dslik/powersim/1840A/1840-0101/latest/pcb_top.png

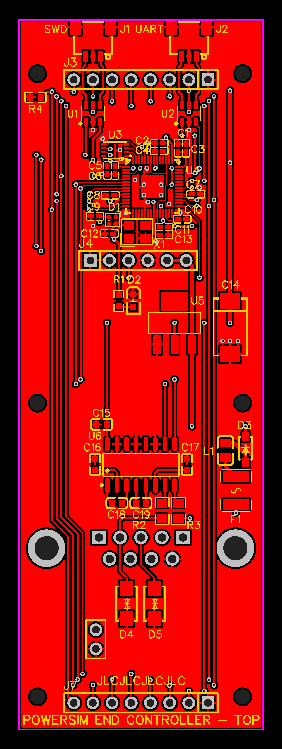
1840A/1840-0101/latest/pcb_top.png
