dslik/powersim/1841A/1841-0101/latest/pcb_top.png

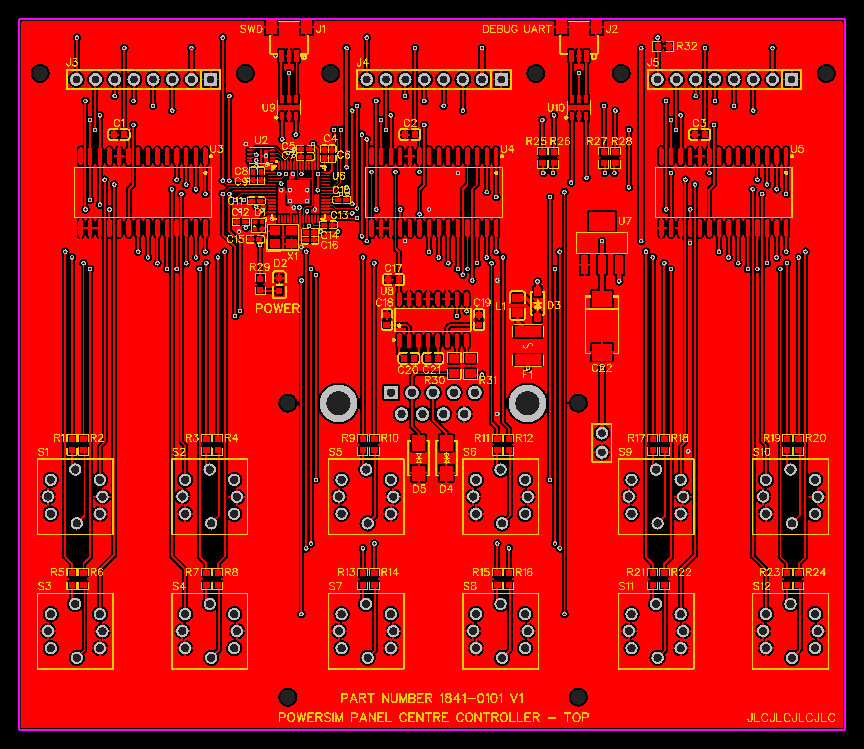
1841A/1841-0101/latest/pcb_top.png
