dslik/powersim/1850A/1850-0201/latest/pcb_top.png

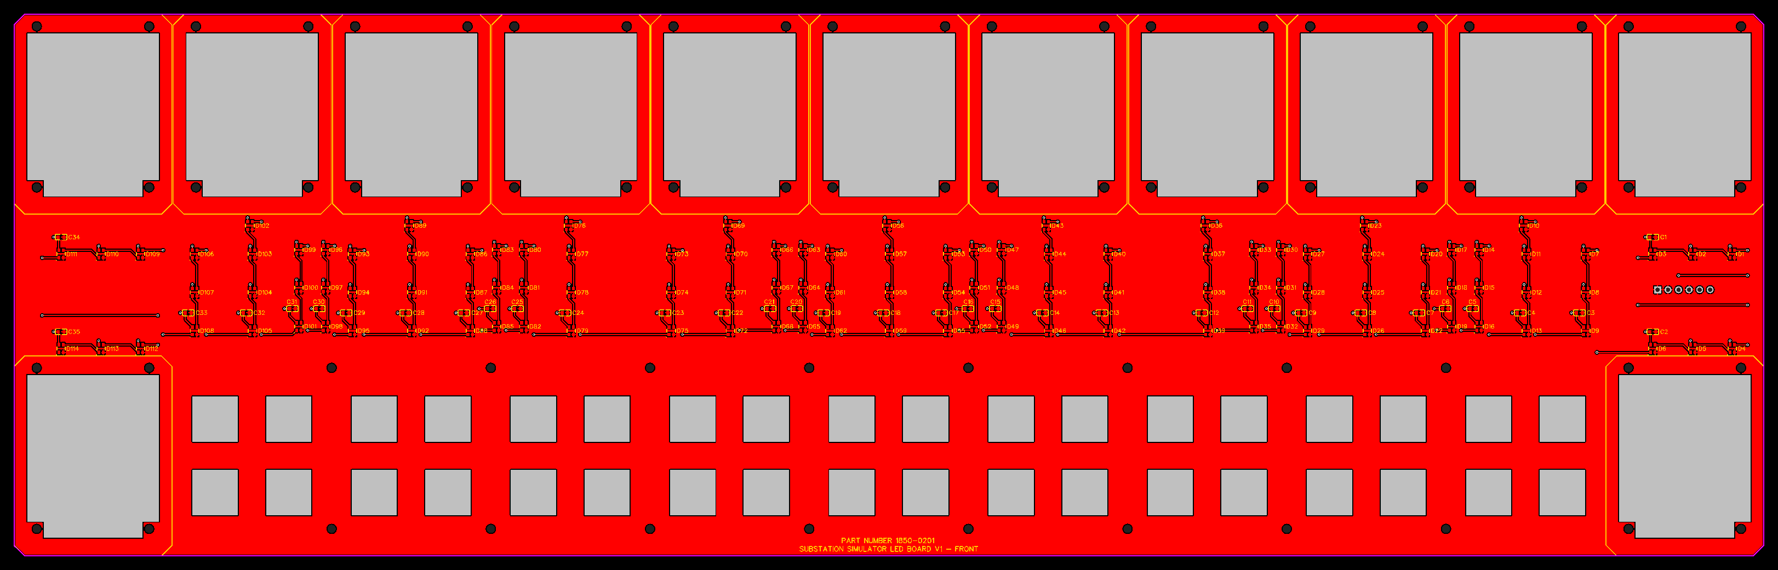
1850A/1850-0201/latest/pcb_top.png
