dslik/powersim/1850A/1850-0201/V1.2/pcb_bottom.png

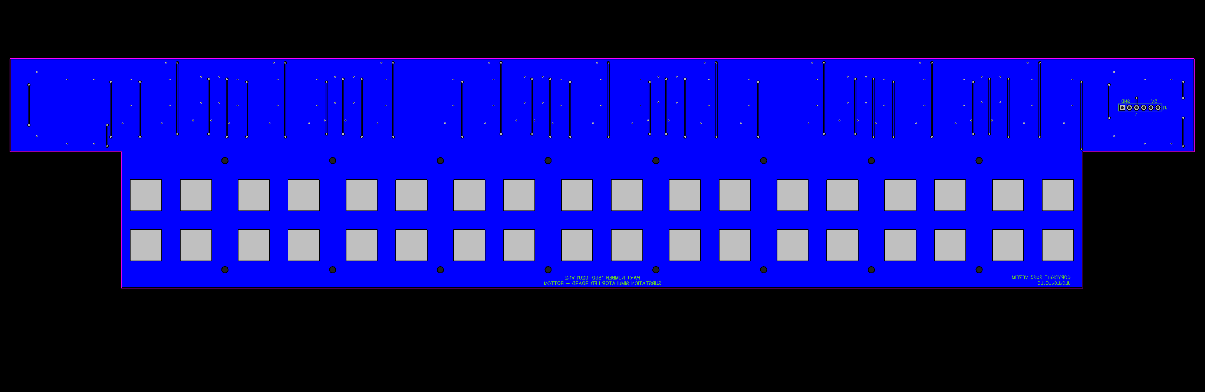
1850A/1850-0201/V1.2/pcb_bottom.png
