dslik/powersim/1850A/1850-0201/V1.2/Produce_DanZhi.SMT_Snapshot.Top.2154951A_Y738.SMT02308291374351.png

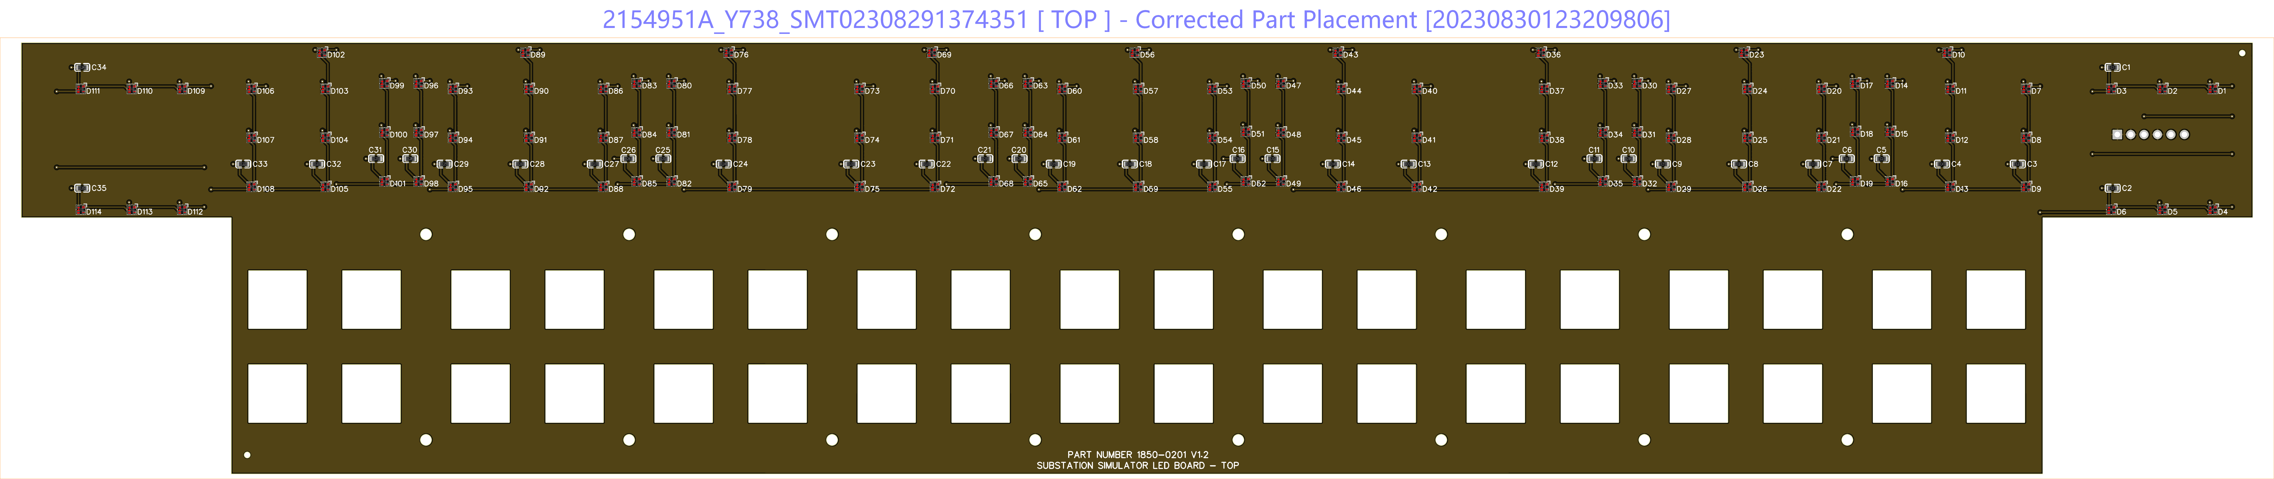
1850A/1850-0201/V1.2/Produce_DanZhi.SMT_Snapshot.Top.2154951A_Y738.SMT02308291374351.png
