dslik/powersim/1850A/1850-0202/latest/pcb_top.png

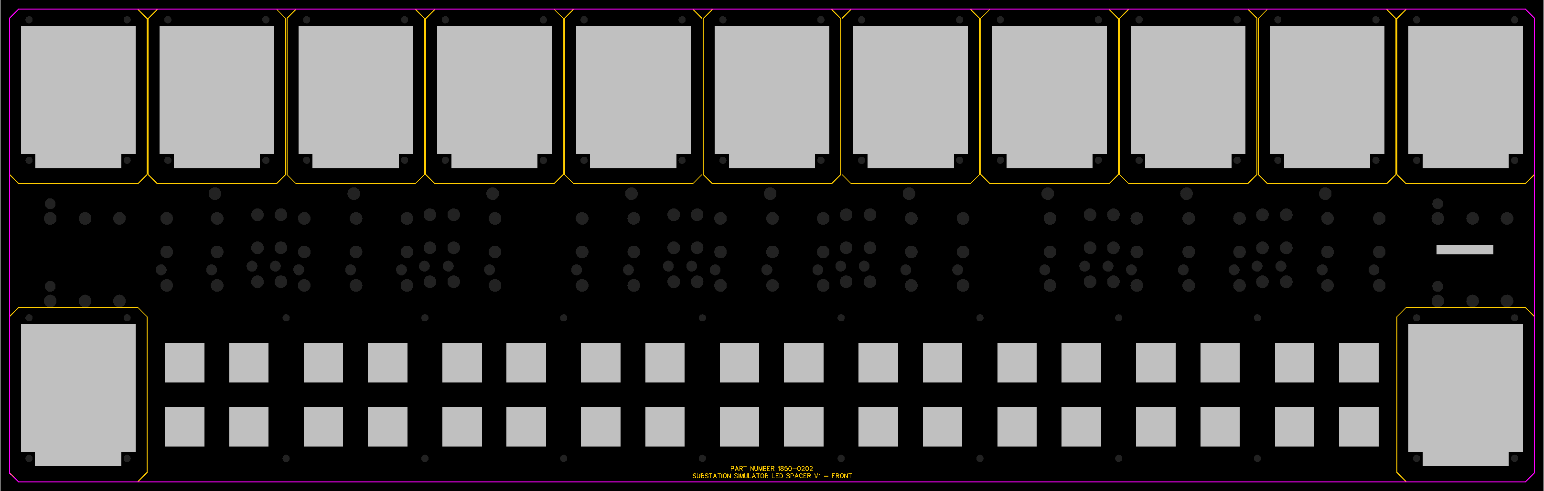
1850A/1850-0202/latest/pcb_top.png
