dslik/powersim/1850A/1850-0203/v0.2/pcb_top.png

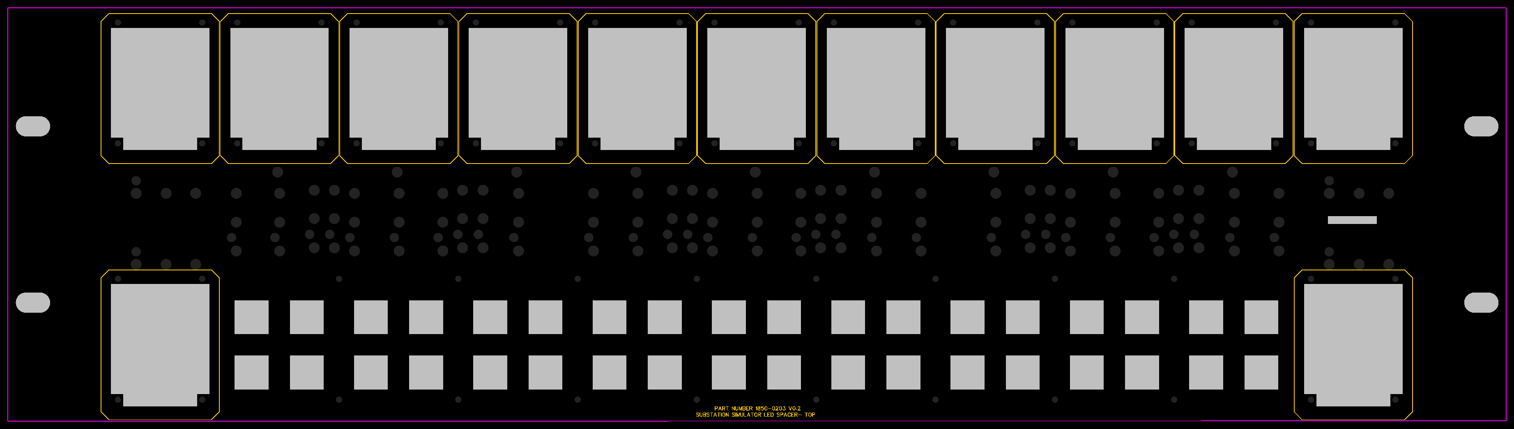
1850A/1850-0203/v0.2/pcb_top.png
