dslik/powersim/1851A/1851-0103/latest/pcb_top.png

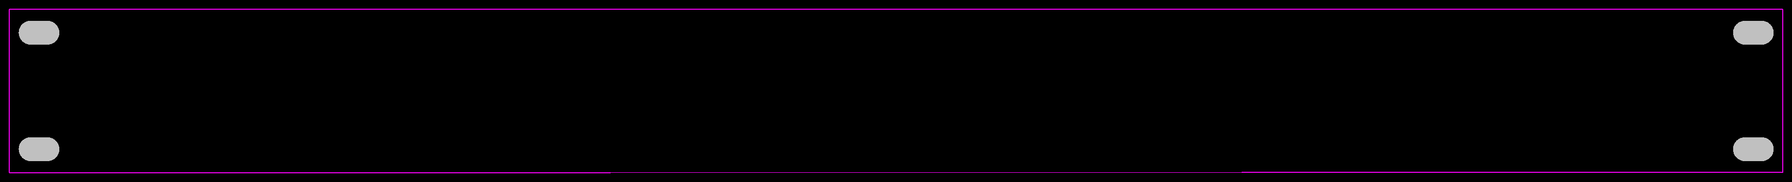
1851A/1851-0103/latest/pcb_top.png
