dslik/powersim/1852A/1852-0101/V0.2/pcb_bottom.png

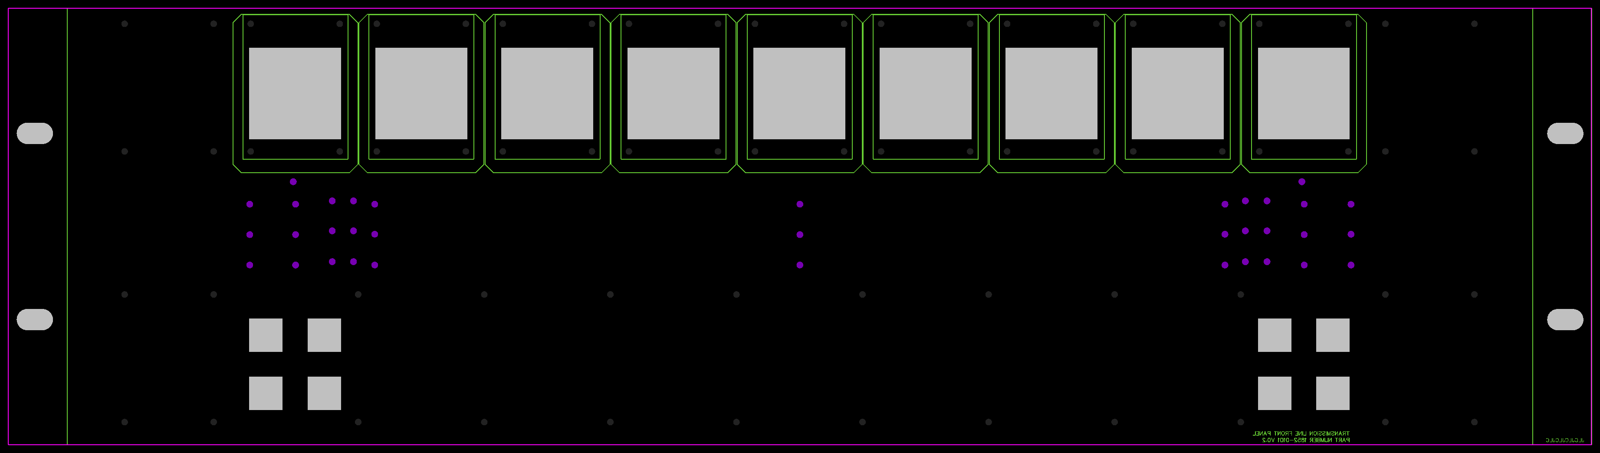
1852A/1852-0101/V0.2/pcb_bottom.png
