dslik/powersim/1853A/1853-0101/latest/pcb_top.png

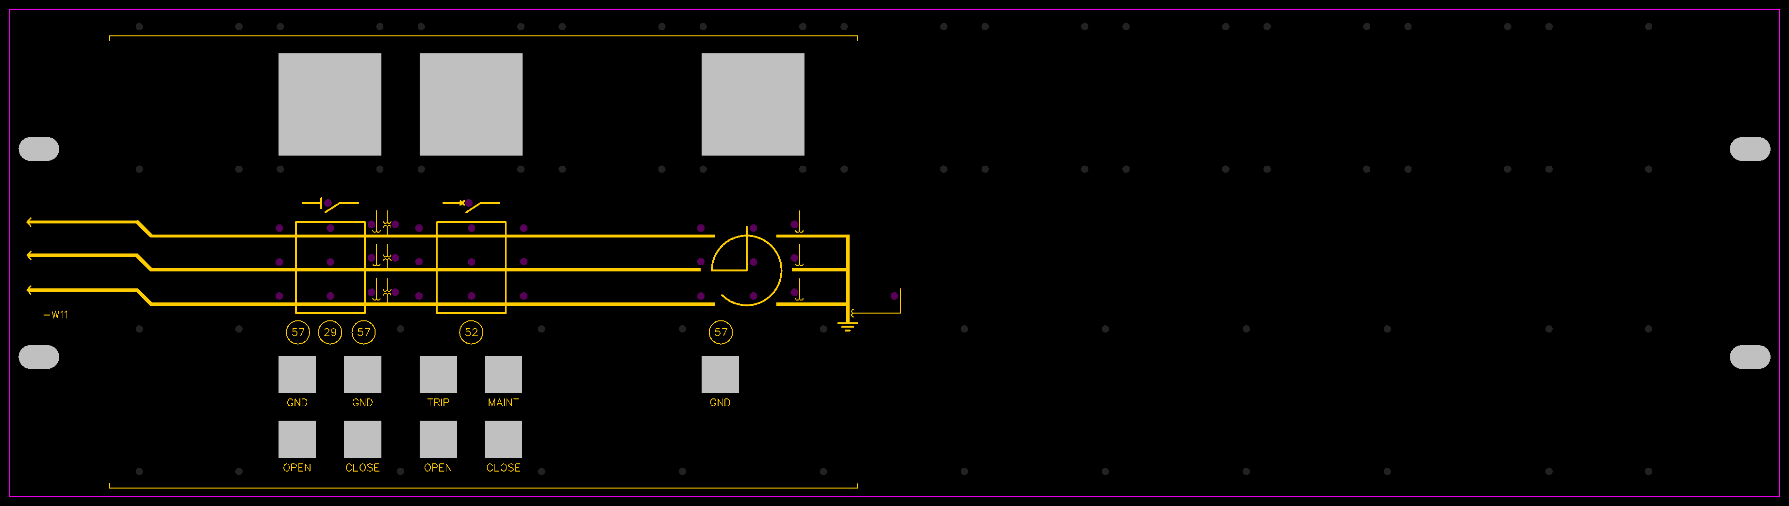
1853A/1853-0101/latest/pcb_top.png
