dslik/powersim/1854A/1854-0101/latest/pcb_top.png

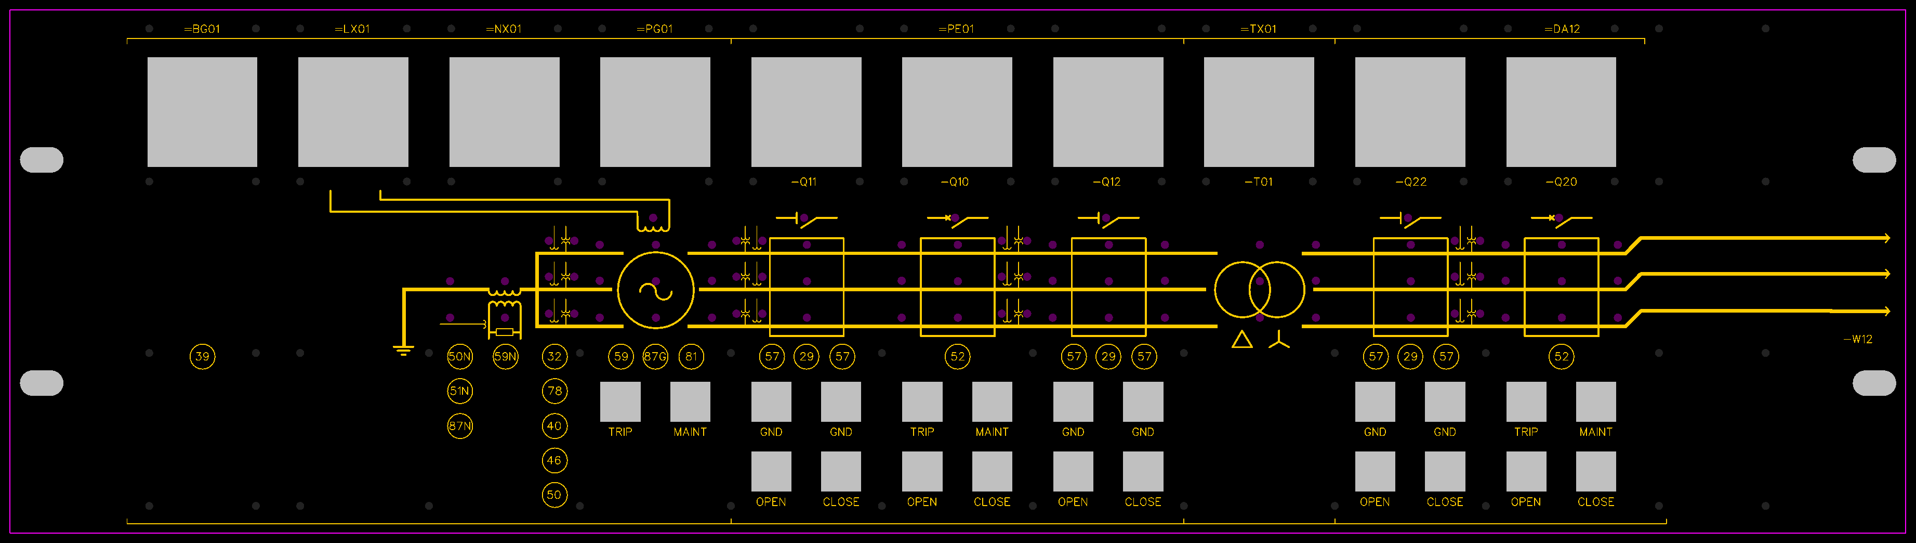
1854A/1854-0101/latest/pcb_top.png
