dslik/powersim/1859A/1859-0101/latest/pcb_top.png

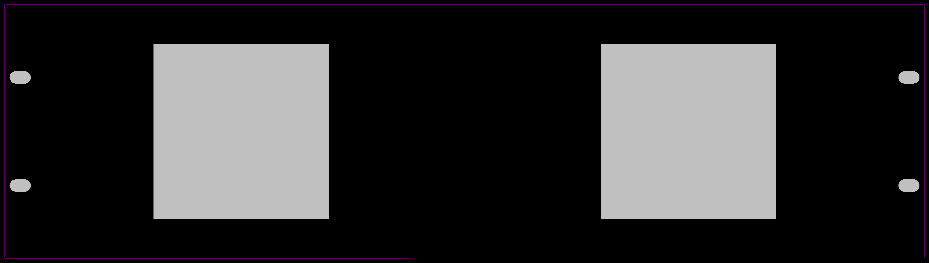
1859A/1859-0101/latest/pcb_top.png
