dslik/powersim/1859A/1859-0101/V0.2/pcb_top.png

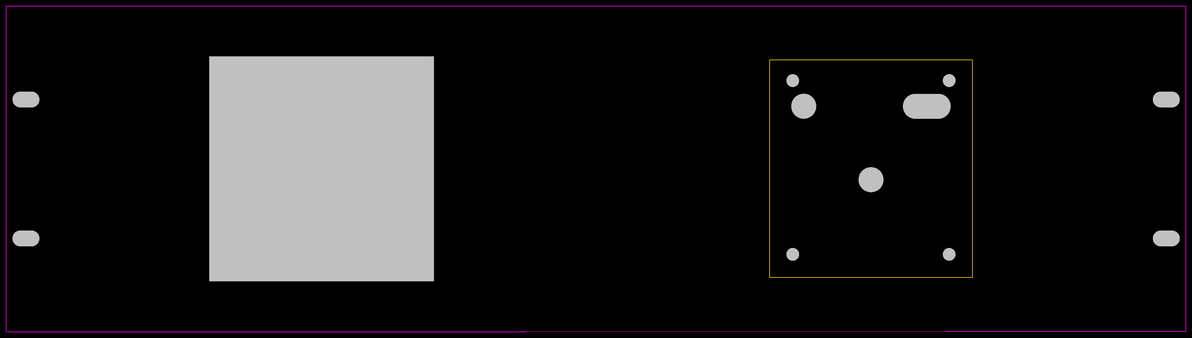
1859A/1859-0101/V0.2/pcb_top.png
