dslik/powersim/1870A/1870-0101/latest/pcb_top.png

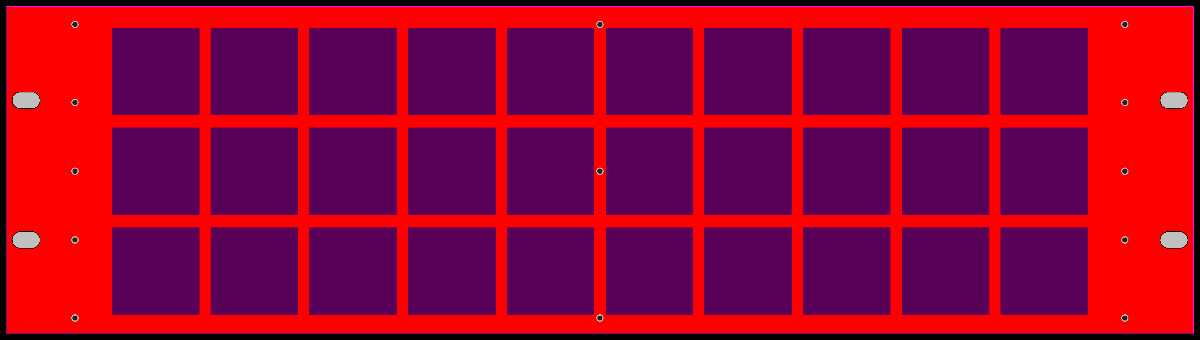
1870A/1870-0101/latest/pcb_top.png
