dslik/powersim/1870A/1870-0101/V0.2/pcb_top.png

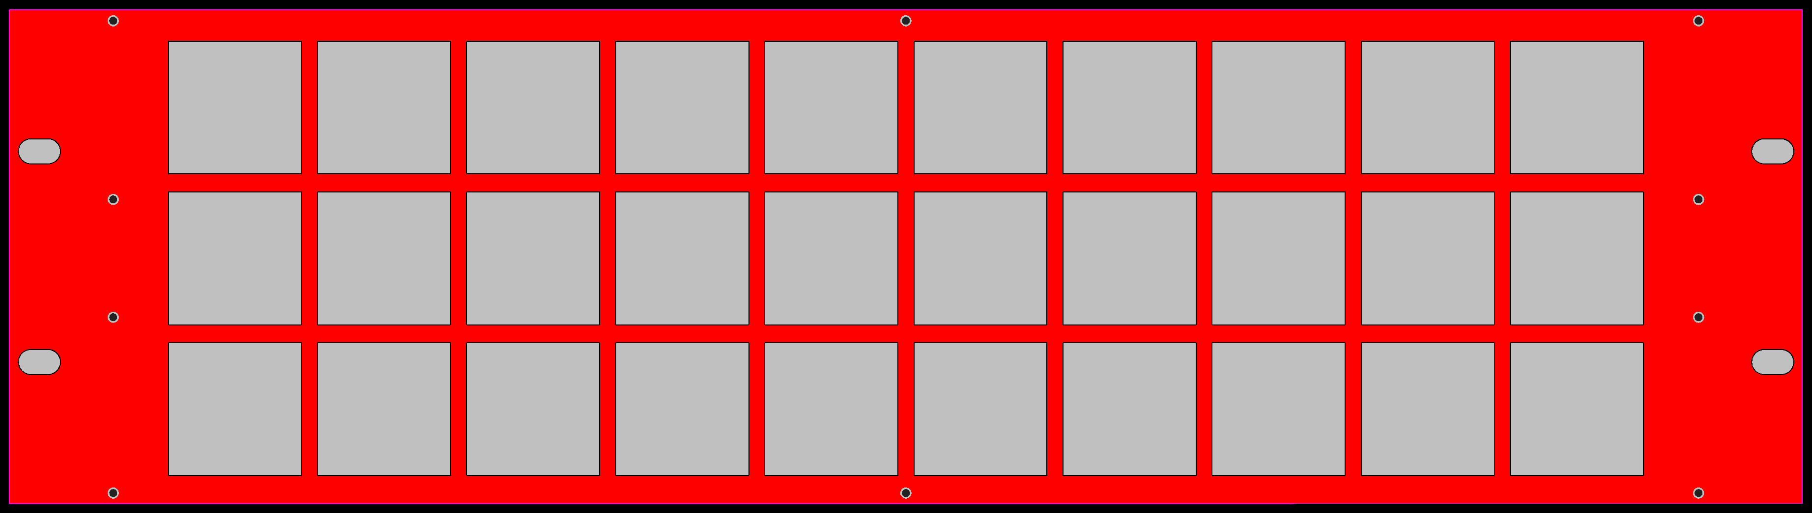
1870A/1870-0101/V0.2/pcb_top.png
