dslik/powersim/1870A/1870-0102/V0.3/pcb_bottom.png

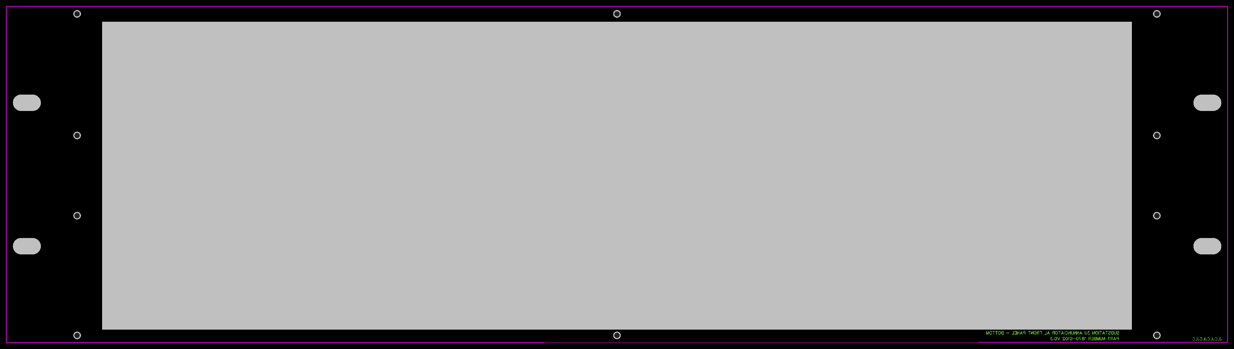
1870A/1870-0102/V0.3/pcb_bottom.png
