dslik/powersim/1870A/1870-0103/latest/pcb_top.png

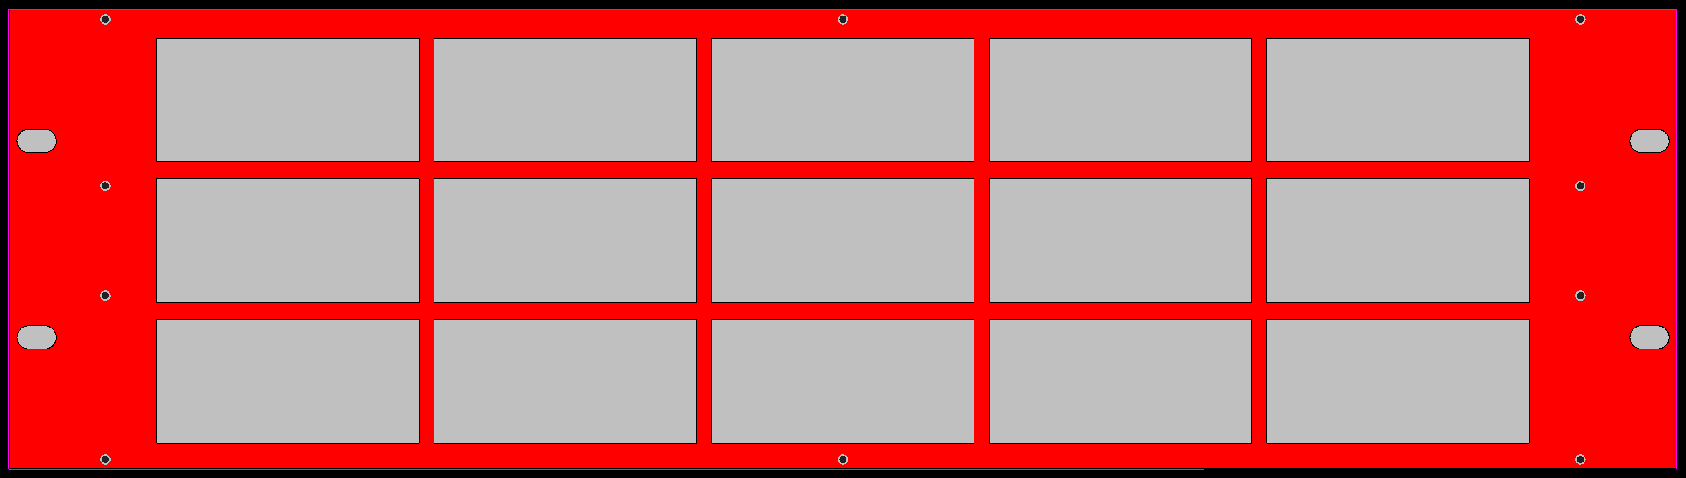
1870A/1870-0103/latest/pcb_top.png
