dslik/powersim/1870A/1870-0201/latest/pcb_top.png

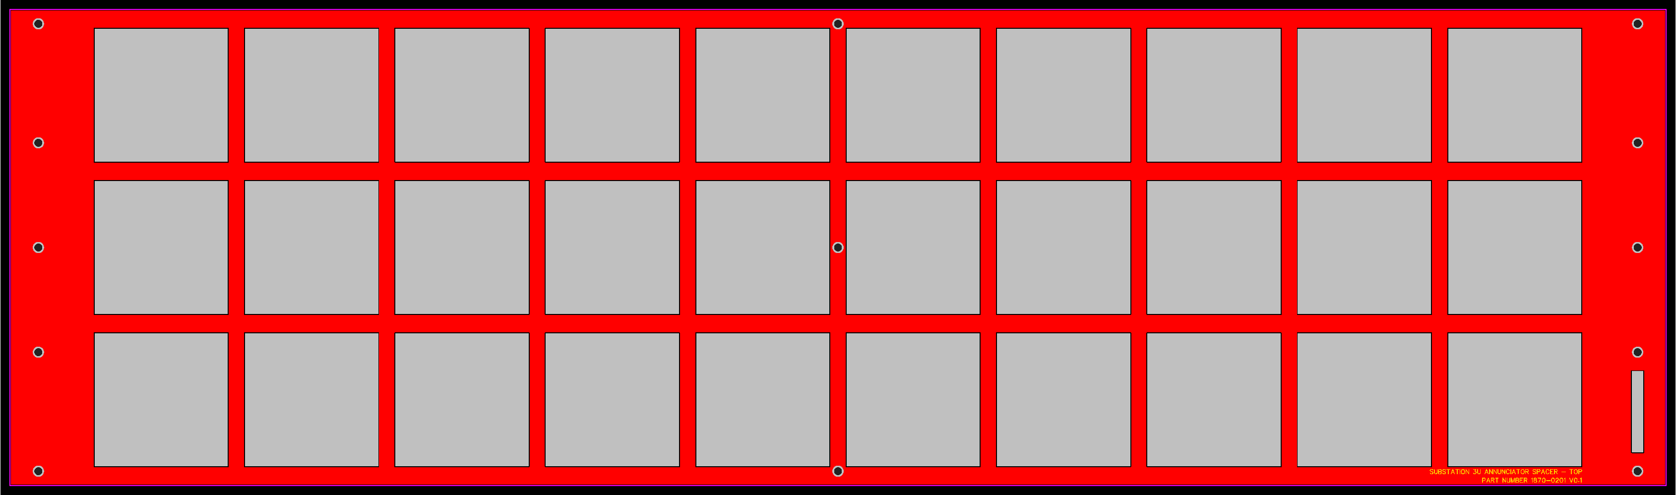
1870A/1870-0201/latest/pcb_top.png
