dslik/powersim/1870A/1870-0203/latest/pcb_bottom.png

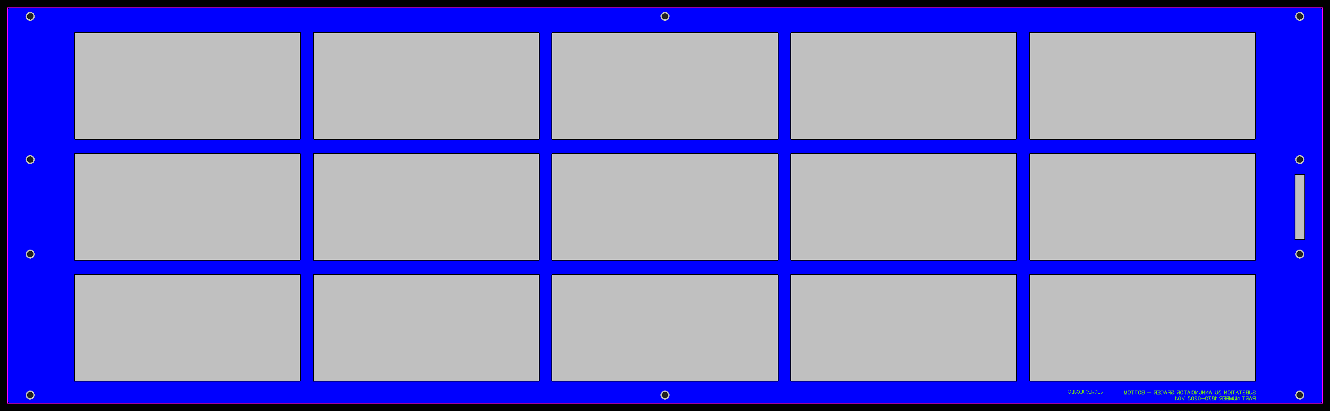
1870A/1870-0203/latest/pcb_bottom.png
