dslik/powersim/1841A/1841-9101/hmi.c

// ---------------------------------------------------------------------------------
// Front panel display routines
// ---------------------------------------------------------------------------------
// Routines for displaying user interfaces on various power simulator front panels
// ---------------------------------------------------------------------------------
// SPDX-FileCopyrightText: Copyright 2023 David Slik (VE7FIM)
// SPDX-FileAttributionText: https://github.com/dslik/powersim/
// SPDX-License-Identifier: CERN-OHL-S-2.0
// ---------------------------------------------------------------------------------
#include <stdio.h>
#include <stdlib.h>
#include <string.h>

#include "pico/stdlib.h"

#include "hmi.h"
#include "fonts.h"
#include "pins.h"
#include "asm_hmi.h"
#include "st7789_lcd.h"
#include "mcp23017.h"
#include "snon/snon_utils.h"
#include "vita40/vita40.h"
#include "pico-utils/ws2812.h"

// Defines
#define FRONT_PANEL_LED_COUNT   108
#define DRAW_TITLE              0b00000001
#define DRAW_PHASE_1            0b00000010
#define DRAW_PHASE_2            0b00000100
#define DRAW_PHASE_3            0b00001000

// Private prototypes
void draw_gen_top_init(void);
void draw_gen_top(uint8_t update_region);
void draw_gen_bottom_init(void);
void draw_gen_bottom(uint8_t update_region);

// Global variables
uint32_t        led_update_counter = 0;
extern uint     pio_sm;
extern uint     pio_sm_offset;
char*           prev_title_time = NULL;
char*           prev_phase1v_time = NULL;
char*           prev_phase2v_time = NULL;
char*           prev_phase3v_time = NULL;
char*           prev_phase1c_time = NULL;
char*           prev_phase2c_time = NULL;
char*           prev_phase3c_time = NULL;

// Functions
void init_gen_screens(void)
{
    draw_gen_top_init();
    draw_gen_bottom_init();
}

void draw_gen_top_init(void)
{
    st7789_start_pixels(PIN_CS_1);

    // Subtitle area
    st7789_set_fgcolor(st7789_rgb_to_colour(asm_text));
    st7789_draw_string_centred("L1", B612_BMA_24, (SCREEN_WIDTH / 3) * 0, (SCREEN_WIDTH / 3) * 1, 160);
    st7789_draw_string_centred("L2", B612_BMA_24, (SCREEN_WIDTH / 3) * 1, (SCREEN_WIDTH / 3) * 2, 160);
    st7789_draw_string_centred("L3", B612_BMA_24, (SCREEN_WIDTH / 3) * 2, (SCREEN_WIDTH / 3) * 3, 160);

    // Flow area
    asm_draw_flow_arrow(1, asm_flow_none);
    asm_draw_flow_arrow(2, asm_flow_none);
    asm_draw_flow_arrow(3, asm_flow_none);

    st7789_end_pixels();

    // Don't display voltages until values received
    prev_phase1v_time = snon_get_time("L1 Voltage");
    prev_phase2v_time = snon_get_time("L2 Voltage");
    prev_phase3v_time = snon_get_time("L3 Voltage");
}

void draw_gen_bottom_init(void)
{
    st7789_start_pixels(PIN_CS_2);

    // Subtitle area
    st7789_set_fgcolor(st7789_rgb_to_colour(asm_text));
    st7789_draw_string_centred("L1", B612_BMA_24, (SCREEN_WIDTH / 3) * 0, (SCREEN_WIDTH / 3) * 1, 160);
    st7789_draw_string_centred("L2", B612_BMA_24, (SCREEN_WIDTH / 3) * 1, (SCREEN_WIDTH / 3) * 2, 160);
    st7789_draw_string_centred("L3", B612_BMA_24, (SCREEN_WIDTH / 3) * 2, (SCREEN_WIDTH / 3) * 3, 160);

    st7789_end_pixels();

    // Don't display currents until values received
    prev_phase1c_time = snon_get_time("L1 Current");
    prev_phase2c_time = snon_get_time("L2 Current");
    prev_phase3c_time = snon_get_time("L3 Current");
}

void update_gen_screens(void)
{
    char* value_time = NULL;

    value_time = snon_get_time("=W01=PHA01");

    if(value_time != prev_title_time)
    {
        draw_gen_top(DRAW_TITLE);
        draw_gen_bottom(DRAW_TITLE);
        prev_title_time = value_time;
    }

    value_time = snon_get_time("L1 Voltage");

    if(value_time != prev_phase1v_time)
    {
        draw_gen_top(DRAW_PHASE_1);
        prev_phase1v_time = value_time;
    }

    value_time = snon_get_time("L2 Voltage");

    if(value_time != prev_phase2v_time)
    {
        draw_gen_top(DRAW_PHASE_2);
        prev_phase2v_time = value_time;
    }

    value_time = snon_get_time("L3 Voltage");

    if(value_time != prev_phase3v_time)
    {
        draw_gen_top(DRAW_PHASE_3);
        prev_phase3v_time = value_time;
    }

    value_time = snon_get_time("L1 Current");

    if(value_time != prev_phase1c_time)
    {
        draw_gen_bottom(DRAW_PHASE_1);
        prev_phase1c_time = value_time;
    }

    value_time = snon_get_time("L2 Current");

    if(value_time != prev_phase2c_time)
    {
        draw_gen_bottom(DRAW_PHASE_2);
        prev_phase2c_time = value_time;
    }

    value_time = snon_get_time("L3 Current");

    if(value_time != prev_phase3c_time)
    {
        draw_gen_bottom(DRAW_PHASE_3);
        prev_phase3c_time = value_time;
    }

//    draw_gen_top();
//    draw_gen_bottom();


}

void draw_gen_top(uint8_t update_region)
{
    st7789_start_pixels(PIN_CS_1);

    // Title area
    if(update_region & DRAW_TITLE)
    {
        st7789_set_fgcolor(st7789_rgb_to_colour(asm_text));
        st7789_draw_string_centred(snon_get_value("=W01=PHA01"), B612_BMA_32, 0, SCREEN_WIDTH, 190);
    }

    // Value indicators
    if(update_region & DRAW_PHASE_1)
    {
        asm_draw_value_indicator(1, snon_get_value_as_double("L1 Voltage LoLo"),
                                    snon_get_value_as_double("L1 Voltage Lo"),
                                    snon_get_value_as_double("L1 Voltage"),
                                    snon_get_value_as_double("L1 Voltage Hi"),
                                    snon_get_value_as_double("L1 Voltage HiHi"),
                                    snon_get_value_as_double("L1 Voltage SP"));

        asm_draw_flow_value(1, snon_get_value_as_double("L1 Voltage"), "V");
    }

    if(update_region & DRAW_PHASE_2)
    {
        asm_draw_value_indicator(2, snon_get_value_as_double("L2 Voltage LoLo"),
                                    snon_get_value_as_double("L2 Voltage Lo"),
                                    snon_get_value_as_double("L2 Voltage"),
                                    snon_get_value_as_double("L2 Voltage Hi"),
                                    snon_get_value_as_double("L2 Voltage HiHi"),
                                    snon_get_value_as_double("L2 Voltage SP"));

        asm_draw_flow_value(2, snon_get_value_as_double("L2 Voltage"), "V");
    }

    if(update_region & DRAW_PHASE_3)
    {
        asm_draw_value_indicator(3, snon_get_value_as_double("L2 Voltage LoLo"),
                                    snon_get_value_as_double("L2 Voltage Lo"),
                                    snon_get_value_as_double("L2 Voltage"),
                                    snon_get_value_as_double("L2 Voltage Hi"),
                                    snon_get_value_as_double("L2 Voltage HiHi"),
                                    snon_get_value_as_double("L2 Voltage SP"));

        asm_draw_flow_value(3, snon_get_value_as_double("L3 Voltage"), "V");
    }

    //asm_draw_value_alarm(2, asm_alarm_one);
    //asm_draw_value_alarm(3, asm_alarm_two);

    st7789_end_pixels();
}

void draw_gen_bottom(uint8_t update_region)
{
    st7789_start_pixels(PIN_CS_2);

    if(update_region & DRAW_TITLE)
    {
        // Title area
        st7789_set_fgcolor(st7789_rgb_to_colour(asm_text));
        st7789_draw_string_centred(snon_get_value("=W01=PHA01"), B612_BMA_32, 0, SCREEN_WIDTH, 190);
    }

    if(update_region & DRAW_PHASE_1)
    {
        // Value indicators
        asm_draw_value_indicator(1, snon_get_value_as_double("L1 Current LoLo"),
                                    snon_get_value_as_double("L1 Current Lo"),
                                    snon_get_value_as_double("L1 Current"),
                                    snon_get_value_as_double("L1 Current Hi"),
                                    snon_get_value_as_double("L1 Current HiHi"),
                                    snon_get_value_as_double("L1 Current SP"));

        asm_draw_flow_value(1, snon_get_value_as_double("L1 Current"), "A");

        // Flow area
        if(snon_get_value_as_double("L1 Current") >=0)
        {
            asm_draw_flow_arrow(1, asm_flow_up);
        }
        else
        {
            asm_draw_flow_arrow(1, asm_flow_down);
        }
    }

    if(update_region & DRAW_PHASE_2)
    {
        // Value indicators
        asm_draw_value_indicator(2, snon_get_value_as_double("L2 Current LoLo"),
                                    snon_get_value_as_double("L2 Current Lo"),
                                    snon_get_value_as_double("L2 Current"),
                                    snon_get_value_as_double("L2 Current Hi"),
                                    snon_get_value_as_double("L2 Current HiHi"),
                                    snon_get_value_as_double("L2 Current SP"));

        asm_draw_flow_value(2, snon_get_value_as_double("L2 Current"), "A");

        // Flow area
        if(snon_get_value_as_double("L2 Current") >=0)
        {
            asm_draw_flow_arrow(2, asm_flow_up);
        }
        else
        {
            asm_draw_flow_arrow(2, asm_flow_down);
        }
    }

    if(update_region & DRAW_PHASE_3)
    {
        asm_draw_value_indicator(3, snon_get_value_as_double("L2 Current LoLo"),
                                    snon_get_value_as_double("L2 Current Lo"),
                                    snon_get_value_as_double("L2 Current"),
                                    snon_get_value_as_double("L2 Current Hi"),
                                    snon_get_value_as_double("L2 Current HiHi"),
                                    snon_get_value_as_double("L2 Current SP"));

        // Value area
        asm_draw_flow_value(3, snon_get_value_as_double("L3 Current"), "A");

        // Flow area
        if(snon_get_value_as_double("L3 Current") >=0)
        {
            asm_draw_flow_arrow(3, asm_flow_up);
        }
        else
        {
            asm_draw_flow_arrow(3, asm_flow_down);
        }
    }

    //asm_draw_value_alarm(2, asm_alarm_one);
    //asm_draw_value_alarm(3, asm_alarm_two);

    st7789_end_pixels();
}


bool draw_gen_leds(struct repeating_timer *t)
{
    uint32_t    led_values[FRONT_PANEL_LED_COUNT];
    uint16_t    counter = 0;

    // Update LED values
    led_values[0] = vita40_to_urgb(snon_get_value("=W01=WBA03=PFA01"), led_update_counter);
    led_values[1] = vita40_to_urgb(snon_get_value("=W01=WBA02=PFA01"), led_update_counter);
    led_values[2] = vita40_to_urgb(snon_get_value("=W01=WBA01=PFA01"), led_update_counter);

    led_values[3] = vita40_to_urgb(snon_get_value("=W01=WBA01=PFA02"), led_update_counter);
    led_values[4] = vita40_to_urgb(snon_get_value("=W01=WBA02=PFA02"), led_update_counter);
    led_values[5] = vita40_to_urgb(snon_get_value("=W01=WBA03=PFA02"), led_update_counter);

    led_values[6] = vita40_to_urgb(snon_get_value("=W01=WBA01=PFA03"), led_update_counter);
    led_values[7] = vita40_to_urgb(snon_get_value("=W01=WBA02=PFA03"), led_update_counter);
    led_values[8] = vita40_to_urgb(snon_get_value("=W01=WBA03=PFA03"), led_update_counter);

    led_values[9] = vita40_to_urgb(snon_get_value("=Q21=PFA01"), led_update_counter);
    led_values[10] = vita40_to_urgb(snon_get_value("=Q21=QBA01=PFA01"), led_update_counter);
    led_values[11] = vita40_to_urgb(snon_get_value("=Q21=QBA02=PFA01"), led_update_counter);
    led_values[12] = vita40_to_urgb(snon_get_value("=Q21=QBA03=PFA01"), led_update_counter);

    led_values[13] = vita40_to_urgb(snon_get_value("=W02=WBA01=PGC01=PFA01"), led_update_counter);
    led_values[14] = vita40_to_urgb(snon_get_value("=W02=WBA02=PGC01=PFA01"), led_update_counter);
    led_values[15] = vita40_to_urgb(snon_get_value("=W02=WBA03=PGC01=PFA01"), led_update_counter);

    led_values[16] = vita40_to_urgb(snon_get_value("=W02=WBA01=PGA01=PFA01"), led_update_counter);
    led_values[17] = vita40_to_urgb(snon_get_value("=W02=WBA02=PGA01=PFA01"), led_update_counter);
    led_values[18] = vita40_to_urgb(snon_get_value("=W02=WBA03=PGA01=PFA01"), led_update_counter);

    led_values[19] = vita40_to_urgb(snon_get_value("=W02=WBA01=PFA01"), led_update_counter);
    led_values[20] = vita40_to_urgb(snon_get_value("=W02=WBA02=PFA01"), led_update_counter);
    led_values[21] = vita40_to_urgb(snon_get_value("=W02=WBA03=PFA01"), led_update_counter);

    led_values[22] = vita40_to_urgb(snon_get_value("=Q20=PFA01"), led_update_counter);
    led_values[23] = vita40_to_urgb(snon_get_value("=Q20=QBA01=PFA01"), led_update_counter);
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
    led_values[69] = vita40_to_urgb(snon_get_value("=Q10=QBA01=PFA01"), led_update_counter);
    led_values[70] = vita40_to_urgb(snon_get_value("=Q10=QBA02=PFA01"), led_update_counter);
    led_values[71] = vita40_to_urgb(snon_get_value("=Q10=QBA03=PFA01"), led_update_counter);

    led_values[72] = vita40_to_urgb(snon_get_value("=W07=WBA01=PFA01"), led_update_counter);
    led_values[73] = vita40_to_urgb(snon_get_value("=W07=WBA02=PFA01"), led_update_counter);
    led_values[74] = vita40_to_urgb(snon_get_value("=W07=WBA03=PFA01"), led_update_counter);

    led_values[75] = vita40_to_urgb(snon_get_value("=Q11=PFA01"), led_update_counter);
    led_values[76] = vita40_to_urgb(snon_get_value("=Q11=QBA01=PFA01"), led_update_counter);
    led_values[77] = vita40_to_urgb(snon_get_value("=Q11=QBA02=PFA01"), led_update_counter);
    led_values[78] = vita40_to_urgb(snon_get_value("=Q11=QBA03=PFA01"), led_update_counter);

    led_values[79] = vita40_to_urgb(snon_get_value("=W08=WBA01=PGC01=PFA01"), led_update_counter);
    led_values[80] = vita40_to_urgb(snon_get_value("=W08=WBA02=PGC01=PFA01"), led_update_counter);
    led_values[81] = vita40_to_urgb(snon_get_value("=W08=WBA03=PGC01=PFA01"), led_update_counter);

    led_values[82] = vita40_to_urgb(snon_get_value("=W08=WBA01=PGA01=PFA01"), led_update_counter);
    led_values[83] = vita40_to_urgb(snon_get_value("=W08=WBA02=PGA01=PFA01"), led_update_counter);
    led_values[84] = vita40_to_urgb(snon_get_value("=W08=WBA03=PGA01=PFA01"), led_update_counter);

    led_values[85] = vita40_to_urgb(snon_get_value("=W08=WBA01=PFA01"), led_update_counter);
    led_values[86] = vita40_to_urgb(snon_get_value("=W08=WBA02=PFA01"), led_update_counter);
    led_values[87] = vita40_to_urgb(snon_get_value("=W08=WBA03=PFA01"), led_update_counter);

    led_values[88] = vita40_to_urgb(snon_get_value("=G01=GAA01=RBA01=PFA01"), led_update_counter);

    led_values[89] = vita40_to_urgb(snon_get_value("=G01=GAA01=PFA01"), led_update_counter);
    led_values[90] = vita40_to_urgb(snon_get_value("=G01=GAA01=PFA02"), led_update_counter);
    led_values[91] = vita40_to_urgb(snon_get_value("=G01=GAA01=PFA03"), led_update_counter);

    led_values[92] = vita40_to_urgb(snon_get_value("=W09=WBA01=PFA01"), led_update_counter);
    led_values[93] = vita40_to_urgb(snon_get_value("=W09=WBA02=PFA01"), led_update_counter);
    led_values[94] = vita40_to_urgb(snon_get_value("=W09=WBA03=PFA01"), led_update_counter);

    led_values[95] = vita40_to_urgb(snon_get_value("=W09=WBA01=PGA01=PFA01"), led_update_counter);
    led_values[96] = vita40_to_urgb(snon_get_value("=W09=WBA02=PGA01=PFA01"), led_update_counter);
    led_values[97] = vita40_to_urgb(snon_get_value("=W09=WBA03=PGA01=PFA01"), led_update_counter);

    led_values[98] = vita40_to_urgb(snon_get_value("=W09=WBA01=PGC01=PFA01"), led_update_counter);
    led_values[99] = vita40_to_urgb(snon_get_value("=W09=WBA02=PGC01=PFA01"), led_update_counter);
    led_values[100] = vita40_to_urgb(snon_get_value("=W09=WBA03=PGC01=PFA01"), led_update_counter);

    led_values[101] = vita40_to_urgb("vita40_off", led_update_counter);
    led_values[102] = vita40_to_urgb("vita40_off", led_update_counter);

    led_values[103] = vita40_to_urgb(snon_get_value("=G01=T02=TAA01=PFA01"), led_update_counter);
    led_values[104] = vita40_to_urgb(snon_get_value("=G01=T02=TAA01=RAC01=PFA01"), led_update_counter);

    led_values[105] = vita40_to_urgb("vita40_off", led_update_counter);

    led_values[106] = vita40_to_urgb(snon_get_value("=W10=WEA01=PFA01"), led_update_counter);
    led_values[107] = vita40_to_urgb(snon_get_value("=G01=T02=TAA01=PGC01=PFA01"), led_update_counter);

    ws2812_program_init(pio1, pio_sm, pio_sm_offset, 18, 800000, false);

    while(counter < FRONT_PANEL_LED_COUNT)
    {
        put_pixel(led_values[counter]);

        counter = counter + 1;
    }

    busy_wait_us(200);

    led_update_counter = led_update_counter + 1;
}


void init_buttons(void)
{
    int         ret = PICO_ERROR_NONE;

    // Note: Initializing in order 1, 2, 3 breaks IRQ handling
    // Note: Initializing in order 3, 2, 1 breaks expander 3 output

    // GPIO Expander #1
    //----------------------------------

    // Configure interrupts
    ret = mcp23017_write_register(i2c1, I2C_ADDR_1, REG_IOCON, 0b01000100);

    // Set all GPIO A I/O lines to be outputs
    ret = mcp23017_write_register(i2c1, I2C_ADDR_1, REG_IODIRA, 0b00000000);
    // Set all GPIO A I/O lines to zero
    ret = mcp23017_write_register(i2c1, I2C_ADDR_1, REG_GPIOA, 0b00000000);

    // Set all GPIO B I/O lines to be inputs
    ret = mcp23017_write_register(i2c1, I2C_ADDR_1, REG_IODIRB, 0b11111111);
    // Enable all GPIO B I/O line pull-up Resistors
    ret = mcp23017_write_register(i2c1, I2C_ADDR_1, REG_GPPUB, 0b11111111);
    // Default value for inputs is all ones
    ret = mcp23017_write_register(i2c1, I2C_ADDR_1, REG_DEFVALB, 0b11111111);
    // Enable INTA for button inputs
    ret = mcp23017_write_register(i2c1, I2C_ADDR_1, REG_GPINTENB, 0b11111111);
    
    // Turn on all LEDs
    ret = mcp23017_write_register(i2c1, I2C_ADDR_1, REG_GPIOA, 0b11111111);

    // GPIO Expander #2
    //----------------------------------

    // Configure interrupts
    ret = mcp23017_write_register(i2c1, I2C_ADDR_2, REG_IOCON, 0b01000100);

    // Set all GPIO A I/O lines to be outputs
    ret = mcp23017_write_register(i2c1, I2C_ADDR_2, REG_IODIRA, 0b00000000);
    // Set all GPIO A I/O lines to zero
    ret = mcp23017_write_register(i2c1, I2C_ADDR_2, REG_GPIOA, 0b00000000);

    // Set all GPIO B I/O lines to be inputs
    ret = mcp23017_write_register(i2c1, I2C_ADDR_2, REG_IODIRB, 0b11111111);
    // Enable all GPIO B I/O line pull-up Resistors
    ret = mcp23017_write_register(i2c1, I2C_ADDR_2, REG_GPPUB, 0b11111111);
    // Default value for inputs is all ones
    ret = mcp23017_write_register(i2c1, I2C_ADDR_2, REG_DEFVALB, 0b11111111);
    // Enable INTA for button inputs
    ret = mcp23017_write_register(i2c1, I2C_ADDR_2, REG_GPINTENB, 0b11111111);
    
    // Turn on all LEDs
    ret = mcp23017_write_register(i2c1, I2C_ADDR_2, REG_GPIOA, 0b11111111);

    // GPIO Expander #3
    //----------------------------------

    // Configure interrupts
    ret = mcp23017_write_register(i2c1, I2C_ADDR_3, REG_IOCON, 0b01000100);

    // Set all GPIO A I/O lines to be outputs
    ret = mcp23017_write_register(i2c1, I2C_ADDR_3, REG_IODIRA, 0b00000000);
    // Set all GPIO A I/O lines to zero
    ret = mcp23017_write_register(i2c1, I2C_ADDR_3, REG_GPIOA, 0b00000000);

    // Set all GPIO B I/O lines to be inputs
    ret = mcp23017_write_register(i2c1, I2C_ADDR_3, REG_IODIRB, 0b11111111);
    // Enable all GPIO B I/O line pull-up Resistors
    ret = mcp23017_write_register(i2c1, I2C_ADDR_3, REG_GPPUB, 0b11111111);
    // Default value for inputs is all ones
    ret = mcp23017_write_register(i2c1, I2C_ADDR_3, REG_DEFVALB, 0b11111111);
    // Enable INTA for button inputs
    ret = mcp23017_write_register(i2c1, I2C_ADDR_3, REG_GPINTENB, 0b11111111);

    // Turn on all LEDs
    ret = mcp23017_write_register(i2c1, I2C_ADDR_3, REG_GPIOA, 0b11111111);

}
