dslik/powersim/1870A/1870-9101/mem_utils.h

// ---------------------------------------------------------------------------------
// Memory utilities - Header
// ---------------------------------------------------------------------------------
// Get free memory
// ---------------------------------------------------------------------------------
// SPDX-FileCopyrightText: Copyright (c) 2021-2023 Christophe "CHiPs44" Petit
// SPDX-FileAttributionText: https://github.com/CHiPs44/hagl_pico_vgaboard/blob/main/example/specs.c
// SPDX-License-Identifier: MIT-0
// ---------------------------------------------------------------------------------
#include <stdlib.h>

size_t get_free_ram_2(void);
